Murrdo/FBG6-3-motors-on-Z-axis/basement/back_left_leg(11).stl

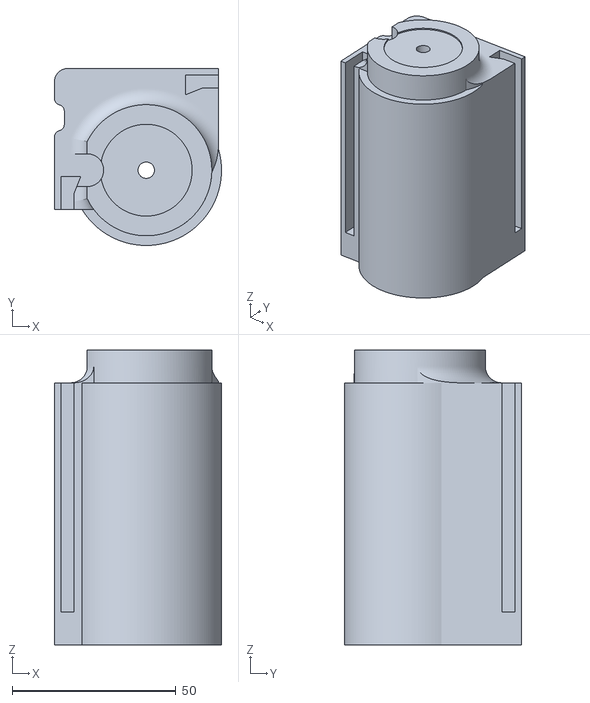
[picture p15: CAD file, 2024-02-22]
basement/back_left_leg(11).stl
51.0 x 54.0 x 90.0
