Murrdo/FBG6-3-motors-on-Z-axis/basement/front_right_leg(5).stl

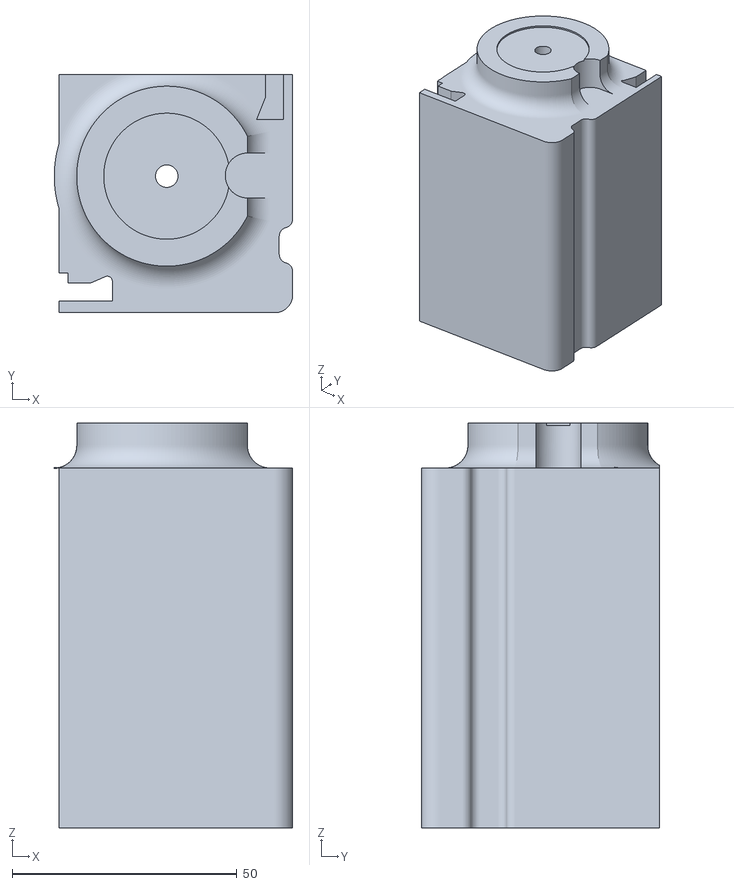
[picture p16: CAD file, 2024-02-22]
basement/front_right_leg(5).stl
53.0 x 53.0 x 90.0
