Murrdo/FBG6-3-motors-on-Z-axis/basement/front_left_leg(8).stl

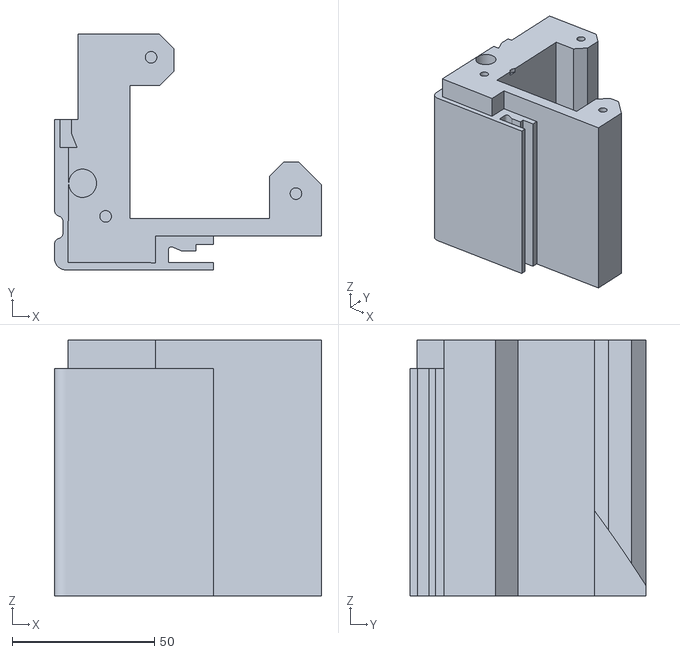
[picture p17: CAD file, 2024-02-22]
basement/front_left_leg(8).stl
94.0 x 83.0 x 90.0
